diaxxu/FMCW-radar/pics/image-26.png

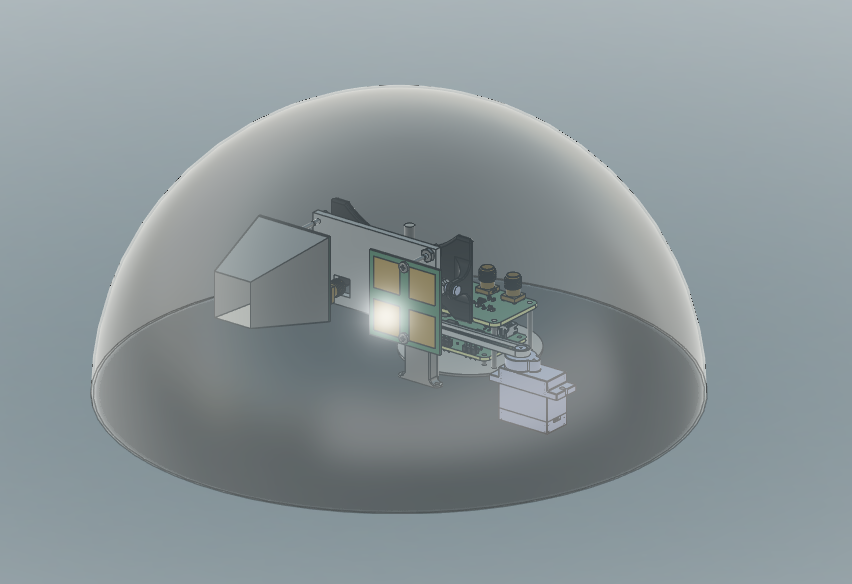
pics/image-26.png
