diaxxu/FMCW-radar/pics/radome.png

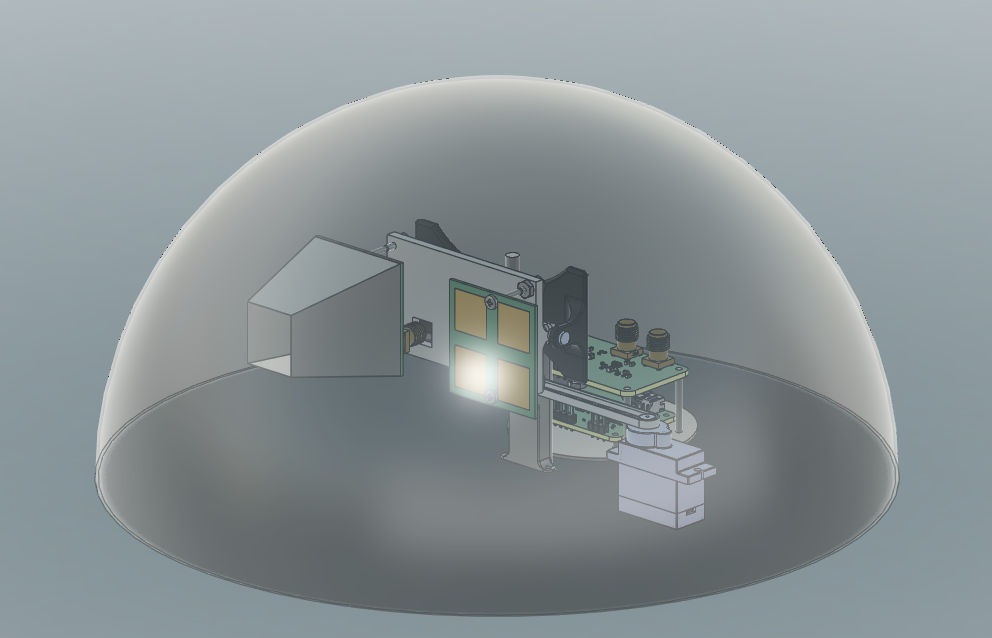
pics/radome.png
